pvandervelde/ha-water-tank-sensor/schematics/tank-sensor.kicad_sch

## KiCad design schematics/tank-sensor.kicad_sch (2025-03-01)

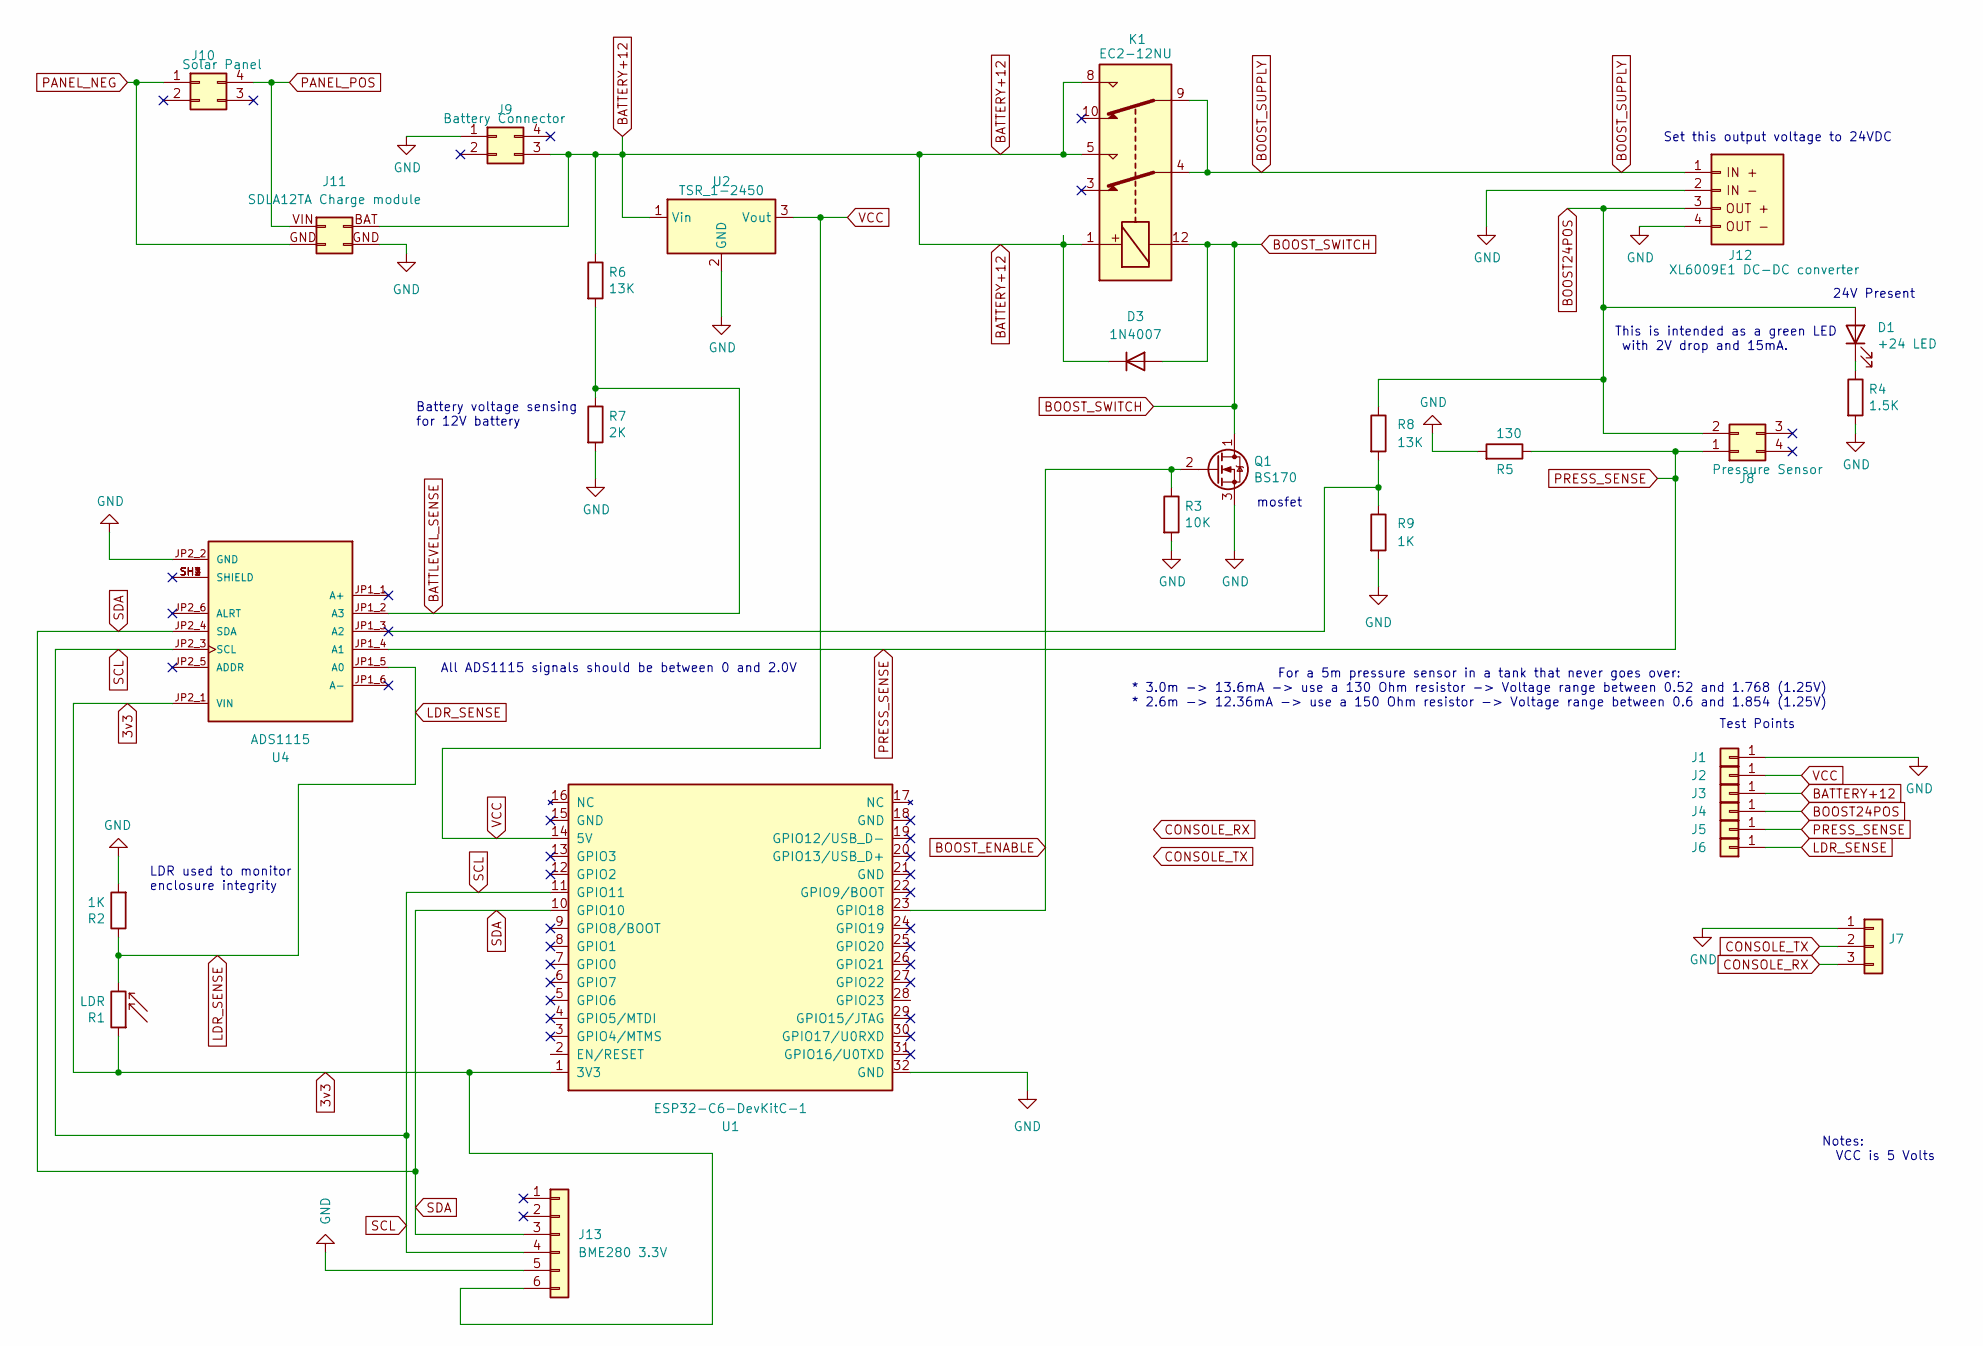
[picture p2: schematic tank-sensor.kicad_sch]

Parts:
D1: +24 LED
D3: 1N4007; D_DO-41_SOD81_P10.16mm_Horizontal
J1, J2, J3, J4, J5, J6, J7: (no value)
J8: Pressure Sensor
J9: Battery Connector
J10: Solar Panel
J11: SDLA12TA Charge module
J12: XL6009E1 DC-DC converter
J13: BME280 3.3V
K1: EC2-12NU
Q1: BS170
R1: LDR
R2, R9: 1K
R3: 10K
R4: 1.5K
R5: 130
R6, R8: 13K
R7: 2K
U1: ESP32-C6-DevKitC-1
U2: TSR_1-2450
U4: ADS1115; MODULE_1085; PARTREV C

Connections:
3v3: J13.6, R1.1, U1.1 (3V3), U4.JP2_1 (VIN)
BATTERY+12: D3.1 (K), J3.1, J9.3, J11.BAT, K1.1, K1.5, K1.8, R6.1, U2.1 (Vin)
BATTLEVEL_SENSE: R6.2, R7.1, U4.JP1_2 (A3)
BOOST24POS: D1.2 (A), J4.1, J8.2, J12.3, R8.1
BOOST_ENABLE: Q1.2 (G), R3.1, U1.23 (GPIO18)
BOOST_SUPPLY: J12.1 (IN_+), K1.4, K1.9
BOOST_SWITCH: D3.2 (A), K1.12, Q1.1 (D)
CONSOLE_RX: J7.3
CONSOLE_TX: J7.2
GND: J1.1, J7.1, J9.1, J11.GND, J12.2, J12.4, J13.5, Q1.3 (S), R2.2, R3.2, R4.2, R5.2, R7.2, R9.2, U1.32 (GND), U2.2 (GND), U4.JP2_2 (GND)
LDR_SENSE: J6.1, R1.2, R2.1, U4.JP1_5 (A0)
unnamed: D1.1 (K), R4.1
unnamed: R8.2, R9.1, U4.JP1_3 (A2)
unnamed: U4.SH1 (SHIELD), U4.SH2 (SHIELD), U4.SH3 (SHIELD), U4.SH4 (SHIELD)
PANEL_NEG: J10.1, J11.GND
PANEL_POS: J10.4, J11.VIN
PRESS_SENSE: J5.1, J8.1, R5.1, U4.JP1_4 (A1)
SCL: J13.4, U1.11 (GPIO11), U4.JP2_3 (SCL)
SDA: J13.3, U1.10 (GPIO10), U4.JP2_4 (SDA)
VCC: J2.1, U1.14 (5V), U2.3 (Vout)

Notes on the sheet:
mosfet
This is intended as a green LED with 2V drop and 15mA.
Set this output voltage to 24VDC
LDR used to monitor enclosure integrity
Test Points
Notes: VCC is 5 Volts
24V Present
All ADS1115 signals should be between 0 and 2.0V
Battery voltage sensing for 12V battery
For a 5m pressure sensor in a tank that never goes over: * 3.0m -> 13.6mA -> use a 130 Ohm resistor -> Voltage range between 0.52 and 1.768 (1.25V) * 2.6m -> 12.36mA -> use a 150 Ohm resistor -> Voltage range between 0.6 and 1.854 (1.25V)
